Synthron/SynPLC/hardware/simulations/analog_in.asc

C1: cap; 10n
C2: cap; 10p
C3: cap; 10n
C4: cap; 10p
I1: current; 0
R1: res; 11k
R2: res; 16k
R3: res; 300
R4: res; 200
U1: LT1013
U2: LT1013
V1: voltage; 24
V2: voltage; 1
Named nets: 0
.dc V2 0 11
