Synthron/SynPLC/hardware/simulations/analog_out.asc

C1: cap; 270p
C2: cap; 270p
R1: res; 100
R2: res; 47
R3: res; 100
R4: res; 10k
R5: res; 10k
R6: res; 100k
R7: res; 20k
R8: res; 20k
R9: res; 100k
R10: res; 100k
U1: LT1013
U2: LT1013
V1: voltage; 24
V2: voltage; SINE(2.5 2.5 1 0 0 0 0)
Named nets: 0, Vin, Vout
Switch between 
CC and CV
.dc V2 0 5 0.1
